sajanajay/Sixth_Sense/mechanical/CAD/Rear_Unit/rear_mount_upper.SLDPRT

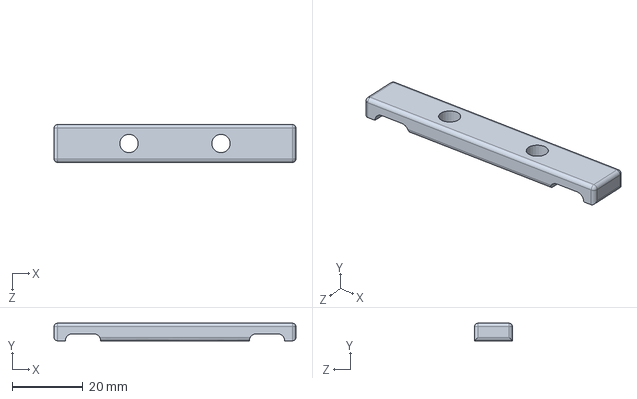
[picture p29: CAD file, 2026-07-05]
mechanical/CAD/Rear_Unit/rear_mount_upper.SLDPRT
68.4 x 5.00 x 10.7 mm
