sajanajay/Sixth_Sense/mechanical/CAD/Front_Unit/front_clamp_lid.SLDPRT

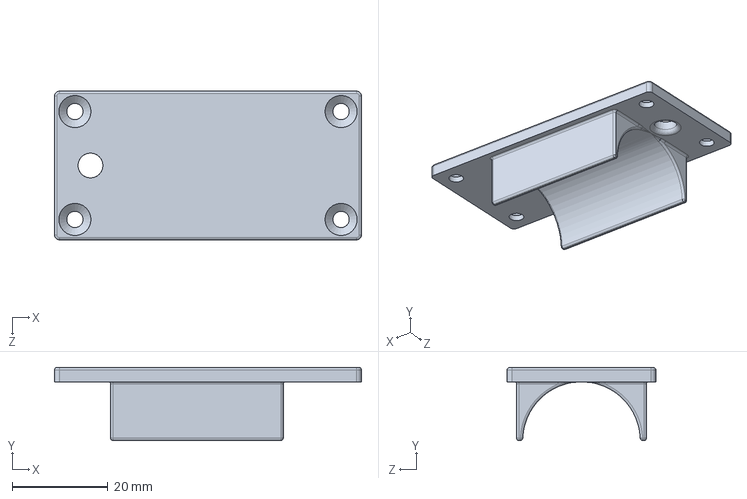
[picture p30: CAD file, 2026-07-05]
mechanical/CAD/Front_Unit/front_clamp_lid.SLDPRT
64.0 x 15.2 x 31.0 mm
