sajanajay/Sixth_Sense/mechanical/CAD/Central_Unit/batteryCase18650x2.step

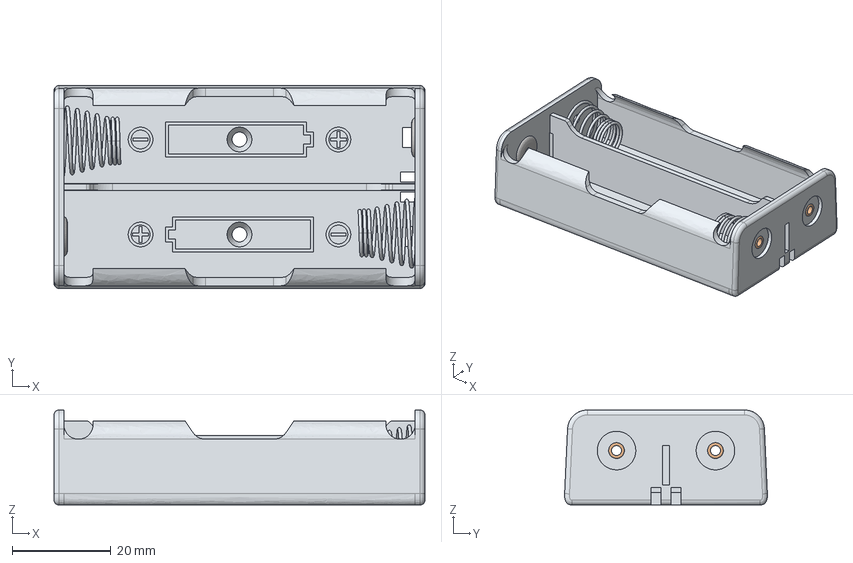
[picture p31: CAD file, 2026-07-05]
mechanical/CAD/Central_Unit/batteryCase18650x2.step
75.0 x 41.0 x 19.2 mm
spring x 2
2_rivets_1
2_rivets_2
positif x 2
