sajanajay/Sixth_Sense/mechanical/CAD/Rear_Unit/rear_mount_lever.SLDPRT

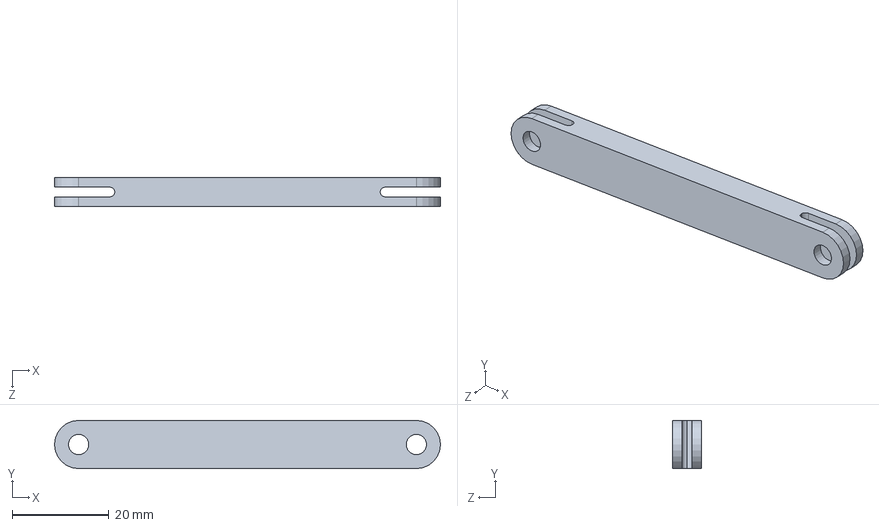
[picture p32: CAD file, 2026-07-05]
mechanical/CAD/Rear_Unit/rear_mount_lever.SLDPRT
80.0 x 10.0 x 6.00 mm
