sajanajay/Sixth_Sense/testing/LTSpice SImulation/Schematic_v1.asc

+8.4V_Power_Rail: voltage; 8.4V
D1: diode; MBRS340
D2: LED; NSPW500BS
ESP_32_IO: voltage; PULSE(0 3.3 0 10n 10n 0.5m 1m)
L1: ind; 1m; Rser=60
M1: nmos; AO3400A
R1: res; 100
R2: res; 10k
R3: res; 330; tol=5
Named nets: 0
.model AO3400A NMOS(Vto=1.45 Kp=30 Lambda=0.01 Rd=0.03)
.tran 10m
LTSpice simulation for vibration motor and LED indicator
